imfrea/mai_pico/doc/io_top.png

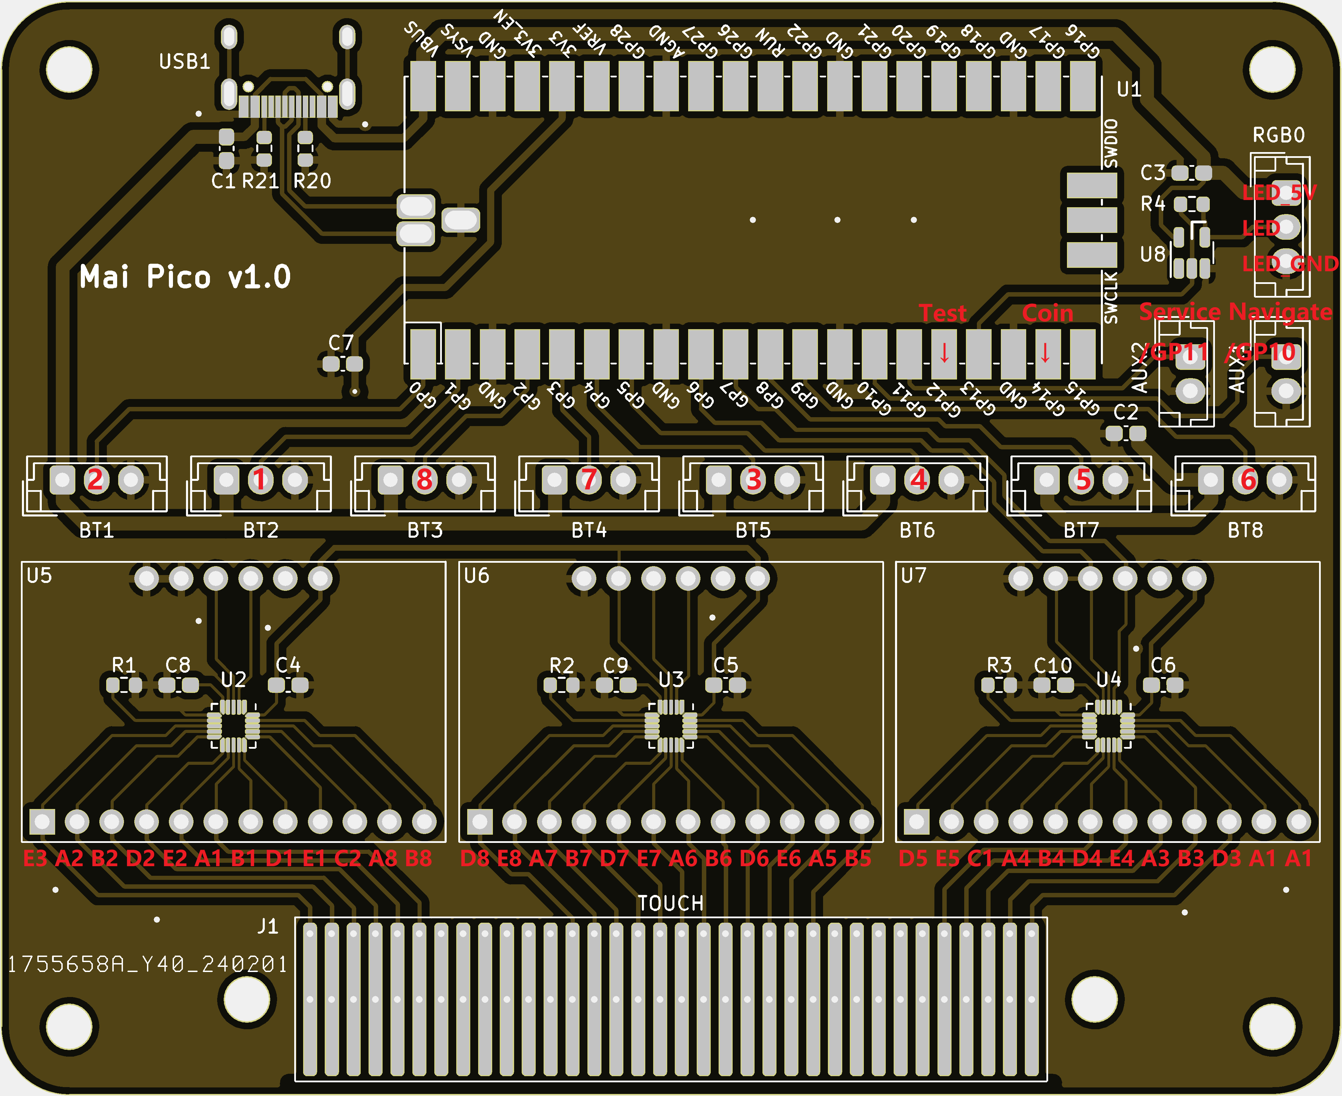
doc/io_top.png
