imfrea/mai_pico/Production/Case/sticker.png

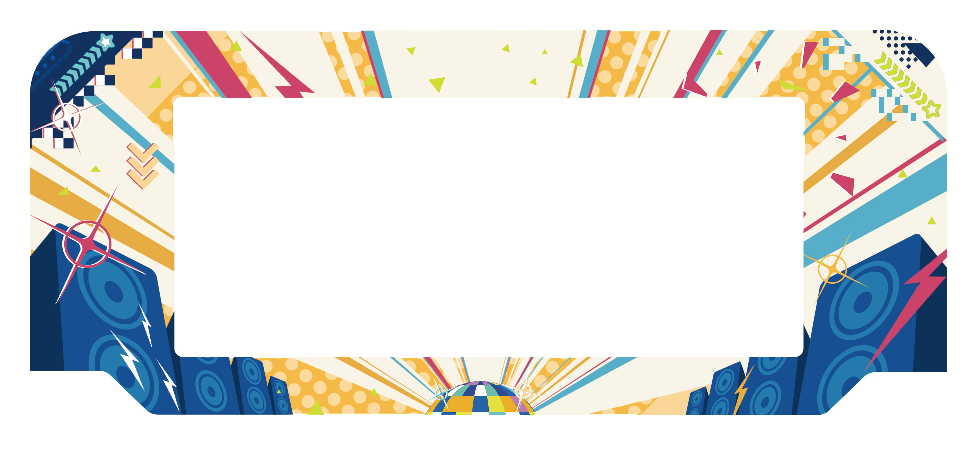
Production/Case/sticker.png
