imfrea/mai_pico/doc/assemble_5_order.jpg

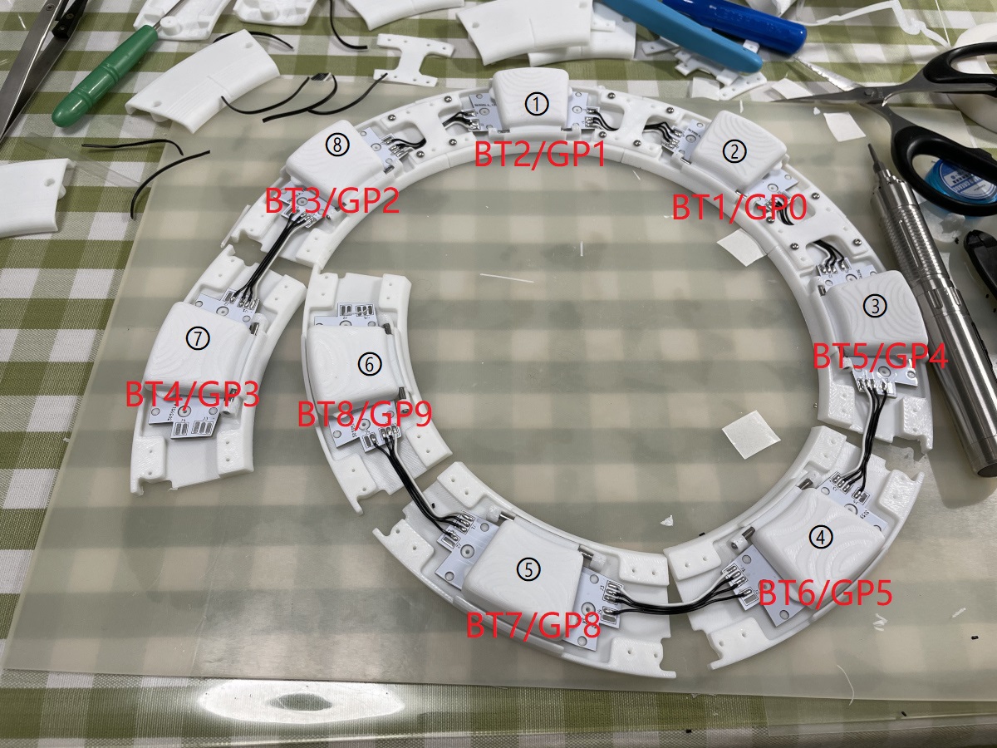
doc/assemble_5_order.jpg
