imfrea/mai_pico/doc/assemble_case_fourth_layer.jpg

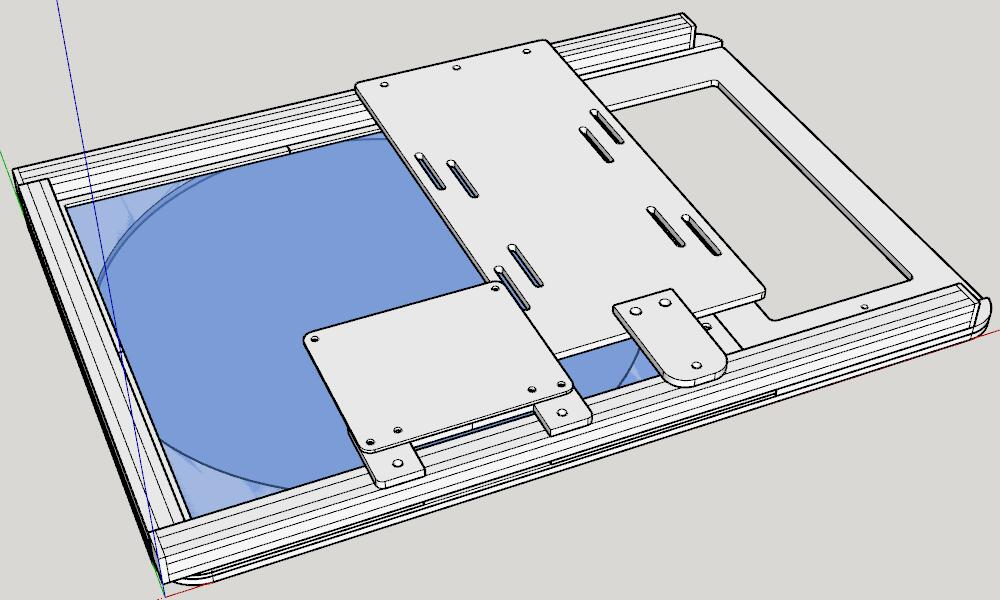
doc/assemble_case_fourth_layer.jpg
