imfrea/mai_pico/doc/assemble_case_second_layer.jpg

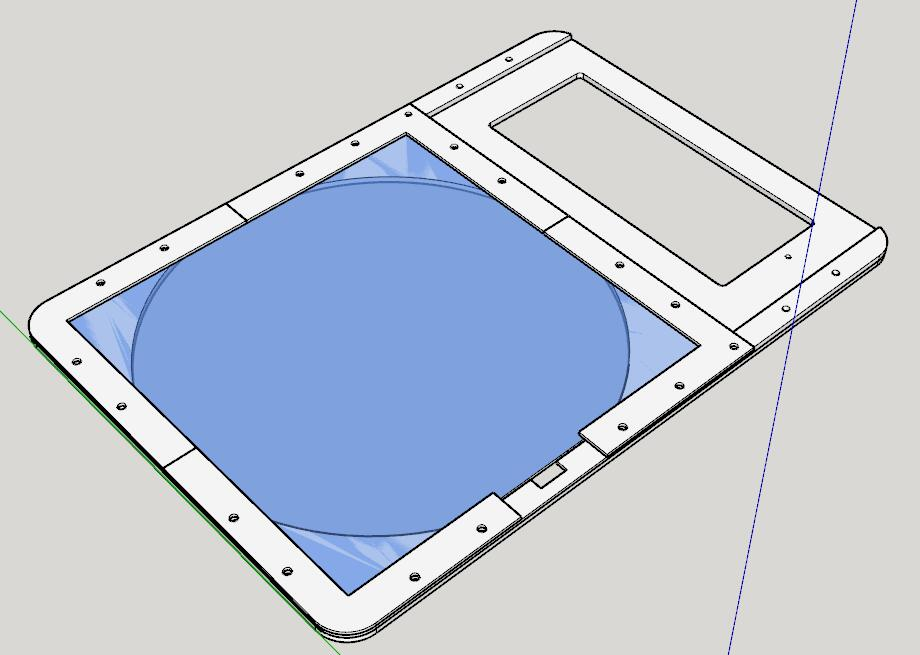
doc/assemble_case_second_layer.jpg
